dimtass/esp8266-web-eload/HelperFunctions.h

/*
 * HelperFunctions.h
 *
 *  Created on: Nov 21, 2018
 *      Author: dimtass
 */

#ifndef HELPERFUNCTIONS_H_
#define HELPERFUNCTIONS_H_

#include <Arduino.h>
#include <SPI.h>
#include <ESP8266WebServer.h>
#include <WebSocketsServer.h>
#include "mcp4x21.h"

#define CS 15

uint8_t            socketNumber;
char               AP_NameChar[11];            // AP_NameString.length() + 1];
const char         WiFiAPPSK[]   = "";        // "put your password here before compiling"
String             AP_NameString = "ESP8266-AP";

ESP8266WebServer server(80);
WebSocketsServer webSocket(81);               // Create a Websocket server
MCP4x21 dac(MCP4x21::ADC_BITS_12);

void spiSendDAC(uint16_t value)
{
	uint16_t conv_val = dac.setADC(value);
	digitalWrite(CS, LOW);
	SPI.transfer16(conv_val);
	digitalWrite(CS, HIGH);
	Serial.print("DAC: "); 	Serial.println(value);
	yield();
}

void handleRoot() {
  server.send(200, "text/html", "<h1>You are connected</h1>");
}

void webSocketEvent(uint8_t num, WStype_t type, uint8_t * payload, size_t lenght) {

  switch (type) {
    case WStype_DISCONNECTED:
      // Reset the control for sending samples of ADC to idle to allow for web server to respond.
      Serial.printf("[%u] Disconnected!\n", num);
      yield();
      break;

    case WStype_CONNECTED: {                  // Braces required http://stackoverflow.com/questions/5685471/error-jump-to-case-label
      IPAddress ip = webSocket.remoteIP(num);
      Serial.printf("[%u] Connected from %d.%d.%d.%d url: %s\n", num, ip[0], ip[1], ip[2], ip[3], payload);
      yield();
      socketNumber = num;
      break;
      }

    case WStype_TEXT:
      if (payload[0] == '#') {
        //Serial.printf("[%u] get Text: %s\n", num, payload);
    	yield();
        if (!(strncmp((char*) &payload[1], "dac=", 4))) {
        	String str((char*) &payload[5]);
        	uint16_t dac_val = (uint16_t)str.toInt();
        	/* send dac value */
        	spiSendDAC(dac_val);
        }
      }
      break;

    case WStype_ERROR:
      Serial.printf("Error [%u] , %s\n", num, payload);
  }
}


String getContentType(String filename) {
  yield();
  if (server.hasArg("download"))      return "application/octet-stream";
  else if (filename.endsWith(".htm")) return "text/html";
  else if (filename.endsWith(".html"))return "text/html";
  else if (filename.endsWith(".css")) return "text/css";
  else if (filename.endsWith(".js"))  return "application/javascript";
  else if (filename.endsWith(".png")) return "image/png";
  else if (filename.endsWith(".gif")) return "image/gif";
  else if (filename.endsWith(".jpg")) return "image/jpeg";
  else if (filename.endsWith(".ico")) return "image/x-icon";
  else if (filename.endsWith(".xml")) return "text/xml";
  else if (filename.endsWith(".pdf")) return "application/x-pdf";
  else if (filename.endsWith(".zip")) return "application/x-zip";
  else if (filename.endsWith(".gz"))  return "application/x-gzip";
  else if (filename.endsWith(".svg")) return "image/svg+xml";
  return "text/plain";
}


bool handleFileRead(String path) {
  Serial.println("handleFileRead: " + path);

  if (path.endsWith("/"))
  {
    path += "index.html";
  }

  String contentType = getContentType(path);
  String pathWithGz = path + ".gz";
  Serial.println("PathFile: " + pathWithGz);

  if (SPIFFS.exists(pathWithGz) || SPIFFS.exists(path))
  {
    if (SPIFFS.exists(pathWithGz)) path += ".gz";
    File file = SPIFFS.open(path, "r");
    yield();
    server.streamFile(file, contentType);
    file.close();
    return true;
  }
  return false;
}


void setupWiFi()
{
  WiFi.mode(WIFI_AP);
  // char AP_NameChar[AP_NameString.length() + 1];
  memset(AP_NameChar, 0, AP_NameString.length() + 1);

  for (unsigned int i = 0; i <AP_NameString.length(); i++)
    AP_NameChar[i] = AP_NameString.charAt(i);
  yield();
  WiFi.softAP(AP_NameChar, WiFiAPPSK);
}


#endif /* HELPERFUNCTIONS_H_ */
